natecermak/unkey/spice/charge_amplifier.asc

C1: cap; 1n
C2: cap; 15n
I1: current; PULSE(-10n 10n 0 1n 1n 1m 2m); AC 1n
R1: res; 4.5
R2: res; 10Meg
U1: TLV9062
V1: voltage; 1.65
V2: voltage; 3.3
Named nets: 0, +3.3V, +1.65V, in-
#.ac dec 10 1 1Meg
.tran 200m
.ic v(in-) = 1.65
