natecermak/unkey/spice/piezo_driver_mcp48cvd21_ada4098.asc

C1: cap; 15n
C2: cap; 15n
R1: res; 1k
R2: res; 18k
R3: res; 100
R4: res; 1k
R5: res; 18k
R6: res; 100
U1: ADA4098-1
U2: LTC6090
V1: voltage; 24
V2: voltage; 24
V3: voltage; SINE(1.214 1.214 10k)
V4: voltage; 1.2814
V8: voltage; 1.2814
Named nets: 0, +24V, -24V, SIG
.tran 2m
