natecermak/unkey/firmware/include/battery.h

// ==================================================================
// battery.h
// Declarations for battery voltage reading and display
// ==================================================================
#ifndef BATTERY_H
#define BATTERY_H

void poll_battery();

#endif
